Noxel43/modeck-mk1/Renders/img2.png

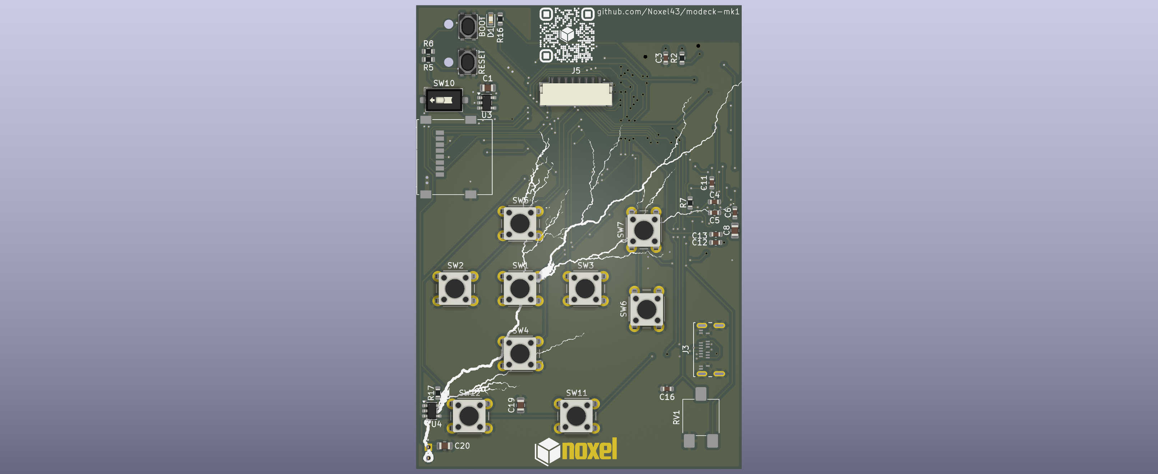
Renders/img2.png
