Noxel43/modeck-mk1/Renders/img3.png

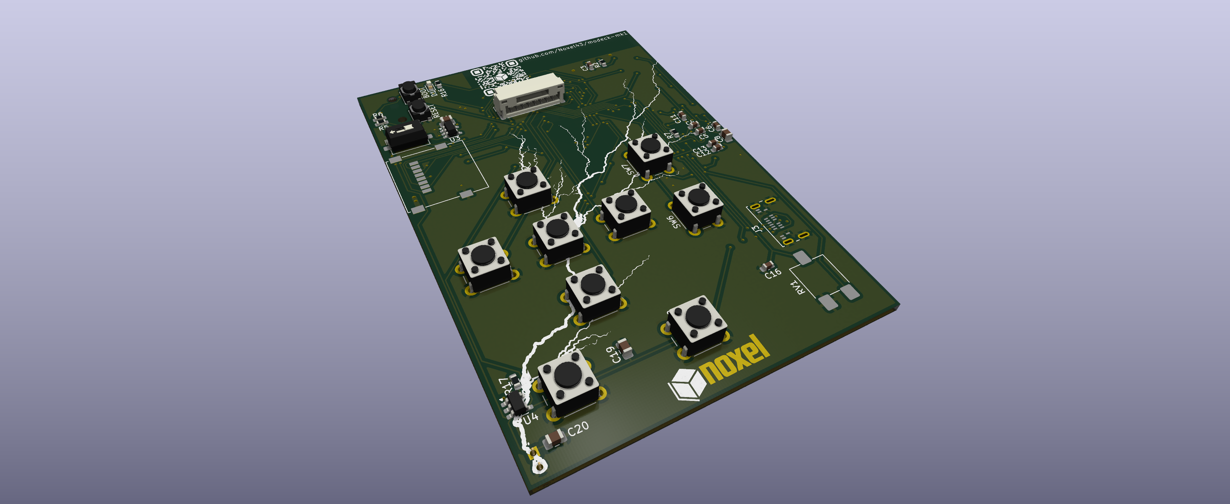
Renders/img3.png
