Noxel43/modeck-mk1/Renders/img4.png

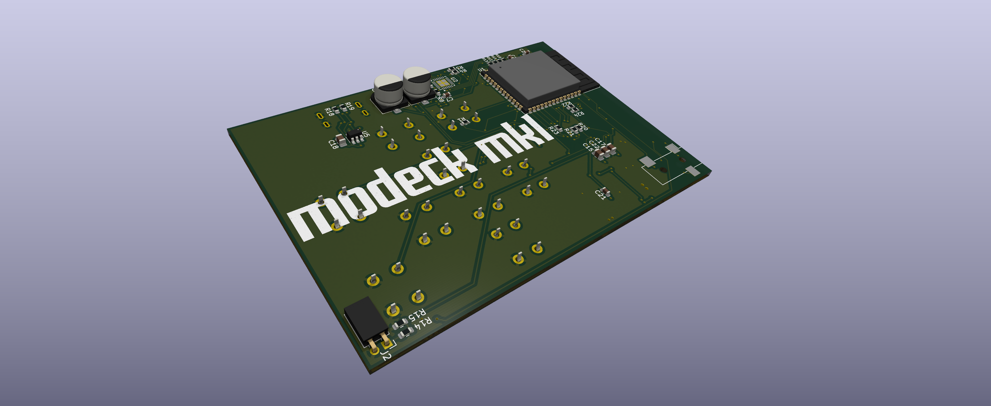
Renders/img4.png
